Sepehr2020/Mechatronics-Design-II/Integration/Tuned/Entire Design/Contact Forces Library/Examples/2D/Cam_Follower/Help/Cam_Follower_Contact_Help_IMAGE.png

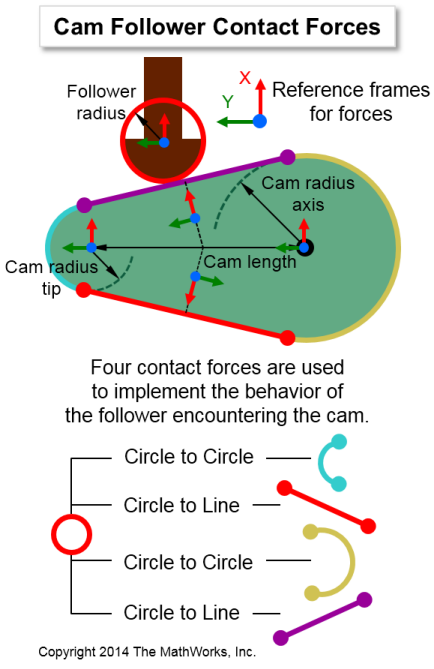
Integration/Tuned/Entire Design/Contact Forces Library/Examples/2D/Cam_Follower/Help/Cam_Follower_Contact_Help_IMAGE.png
