Sepehr2020/Mechatronics-Design-II/Integration/Tuned/Entire Design/Contact Forces Library/Examples/2D/Geneva_Drive/Help/Geneva_Drive_Contact_Shld_Gtip_Help_IMAGE.png

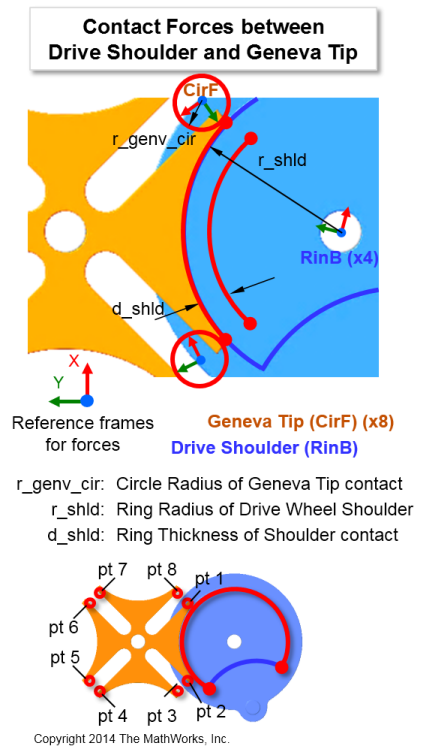
Integration/Tuned/Entire Design/Contact Forces Library/Examples/2D/Geneva_Drive/Help/Geneva_Drive_Contact_Shld_Gtip_Help_IMAGE.png
