Sepehr2020/Mechatronics-Design-II/Integration/Tuned/Entire Design/Contact Forces Library/Examples/2D/Geneva_Drive/Images/Contact_Diagram_DPin_to_GSlot_IMAGE.jpg

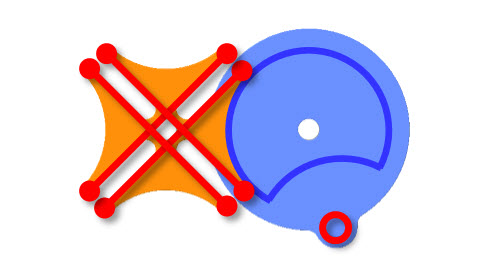
Integration/Tuned/Entire Design/Contact Forces Library/Examples/2D/Geneva_Drive/Images/Contact_Diagram_DPin_to_GSlot_IMAGE.jpg
