Sepehr2020/Mechatronics-Design-II/Integration/Tuned/Entire Design/Contact Forces Library/Examples/2D/Geneva_Drive/Images/Contact_Diagram_Gtip_to_Shld_IMAGE.jpg

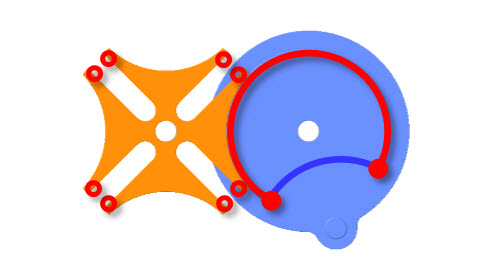
Integration/Tuned/Entire Design/Contact Forces Library/Examples/2D/Geneva_Drive/Images/Contact_Diagram_Gtip_to_Shld_IMAGE.jpg
