Sepehr2020/Mechatronics-Design-II/Integration/Tuned/Entire Design/Contact Forces Library/Examples/2D/Geneva_Drive/Images/Contact_Diagram_Shld_to_GArc_IMAGE.jpg

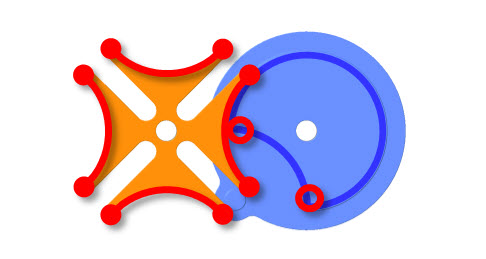
Integration/Tuned/Entire Design/Contact Forces Library/Examples/2D/Geneva_Drive/Images/Contact_Diagram_Shld_to_GArc_IMAGE.jpg
