Sepehr2020/Mechatronics-Design-II/Integration/Tuned/Entire Design/Contact Forces Library/Examples/2D/Mini_Golf/Images/Base_Shoot_IMAGE.jpg

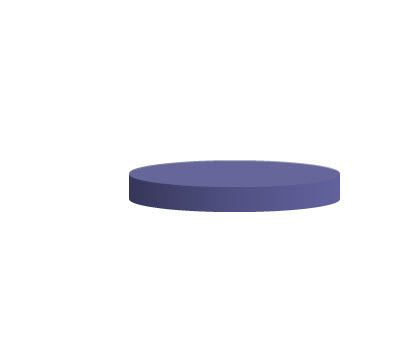
Integration/Tuned/Entire Design/Contact Forces Library/Examples/2D/Mini_Golf/Images/Base_Shoot_IMAGE.jpg
