Sepehr2020/Mechatronics-Design-II/Integration/Tuned/Entire Design/Contact Forces Library/Examples/2D/Mini_Golf/Images/Hole_8_IMAGE.jpg

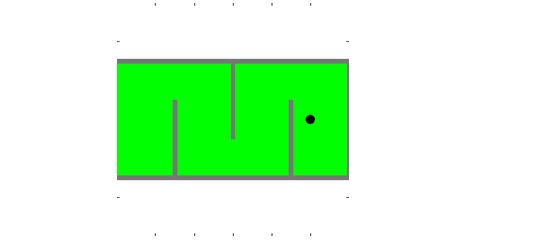
Integration/Tuned/Entire Design/Contact Forces Library/Examples/2D/Mini_Golf/Images/Hole_8_IMAGE.jpg
