Sepehr2020/Mechatronics-Design-II/Integration/Tuned/Entire Design/Contact Forces Library/Examples/3D/Robot_6Legs_4Bar/Images/sm_robot_6legs_4bar_Linkage_Right_IMAGE.png

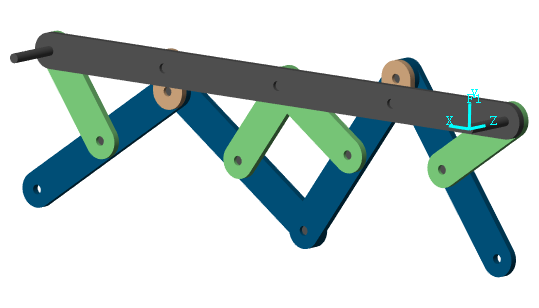
Integration/Tuned/Entire Design/Contact Forces Library/Examples/3D/Robot_6Legs_4Bar/Images/sm_robot_6legs_4bar_Linkage_Right_IMAGE.png
