Sepehr2020/Mechatronics-Design-II/Electronics:Control/Simulation/uppershaft.SLDPRT

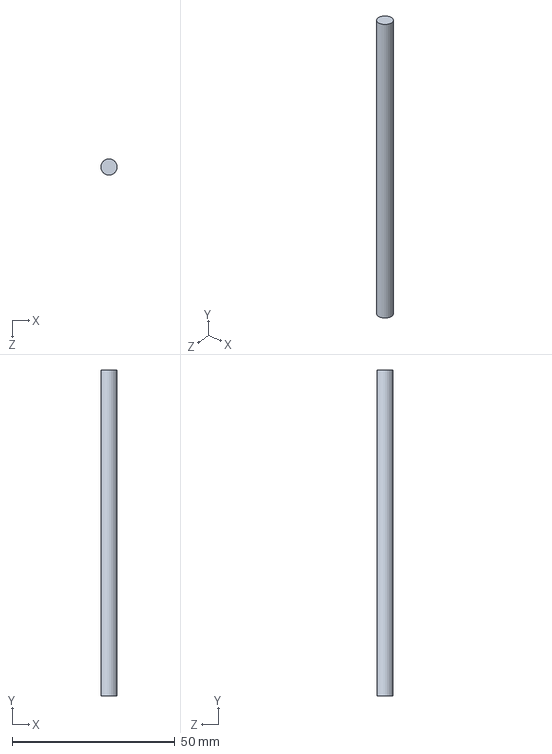
[picture p117: CAD file, 2023-10-18]
Electronics:Control/Simulation/uppershaft.SLDPRT
5.00 x 100.0 x 5.00 mm
