Sepehr2020/Mechatronics-Design-II/Integration/Tuned/Entire Design/Contact Forces Library/Examples/2D/Ball_Bearing/Images/sm_ball_bearing_testrig_ball_constraints_IMAGE.png

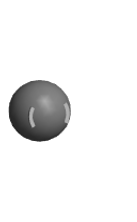
Integration/Tuned/Entire Design/Contact Forces Library/Examples/2D/Ball_Bearing/Images/sm_ball_bearing_testrig_ball_constraints_IMAGE.png
